manayparikh1/sursense/hardware/sursense.kicad_sch

## KiCad design hardware/sursense.kicad_sch (2026-08-20)

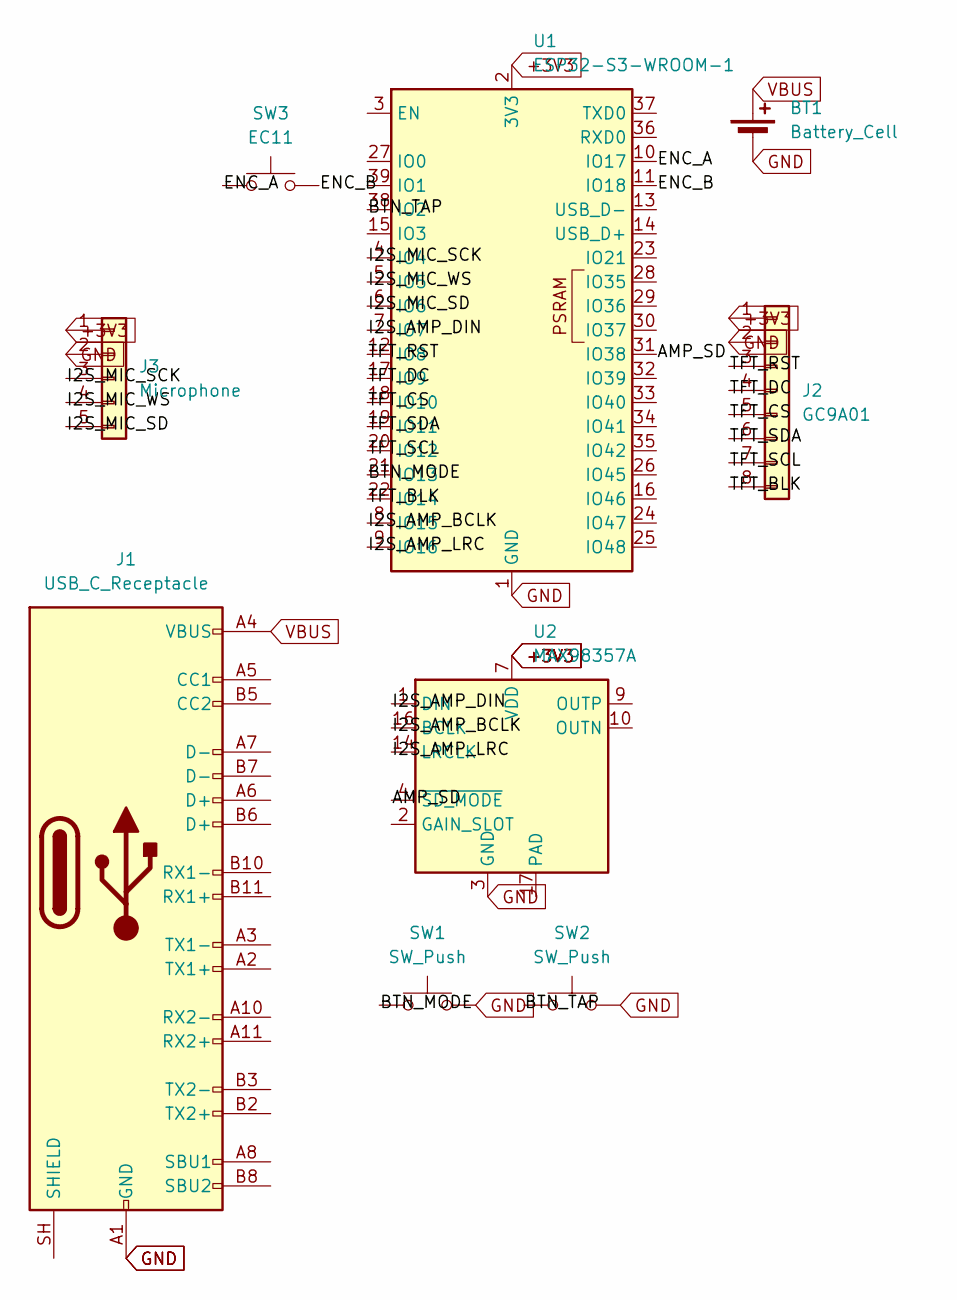
[picture p10: schematic sursense.kicad_sch]

Parts:
BT1: Battery_Cell
J1: USB_C_Receptacle
J2: GC9A01
J3: Microphone
SW1, SW2: SW_Push
SW3: EC11
U1: ESP32-S3-WROOM-1
U2: MAX98357A; TQFN-16-1EP_3x3mm_P0.5mm_EP1.23x1.23mm

Connections:
+3V3: J2.1, J3.1, U1.2 (3V3), U2.7 (VDD), U2.8 (VDD)
AMP_SD: U1.31 (IO38), U2.4 (~SD_MODE)
BTN_MODE: SW1.1, U1.21 (IO13)
BTN_TAP: SW2.1, U1.38 (IO2)
ENC_A: SW3.1, U1.10 (IO17)
ENC_B: SW3.2, U1.11 (IO18)
GND: BT1.2 (-), J1.A1 (GND), J1.A12 (GND), J1.B1 (GND), J1.B12 (GND), J2.2, J3.2, SW1.2, SW2.2, U1.1 (GND), U1.40 (GND), U1.41 (GND), U2.3 (GND), U2.11 (GND), U2.15 (GND)
I2S_AMP_BCLK: U1.8 (IO15), U2.16 (BCLK)
I2S_AMP_DIN: U1.7 (IO7), U2.1 (DIN)
I2S_AMP_LRC: U1.9 (IO16), U2.14 (LRCLK)
I2S_MIC_SCK: J3.3, U1.4 (IO4)
I2S_MIC_SD: J3.5, U1.6 (IO6)
I2S_MIC_WS: J3.4, U1.5 (IO5)
TFT_BLK: J2.8, U1.22 (IO14)
TFT_CS: J2.5, U1.18 (IO10)
TFT_DC: J2.4, U1.17 (IO9)
TFT_RST: J2.3, U1.12 (IO8)
TFT_SCL: J2.7, U1.20 (IO12)
TFT_SDA: J2.6, U1.19 (IO11)
VBUS: BT1.1 (+), J1.A4 (VBUS), J1.A9 (VBUS), J1.B4 (VBUS), J1.B9 (VBUS)
